mrknockknockgaming-droid/hvac-monitor/design/fullscope-home-mockup.html

Continuous diagnostics & control

HomeMain floor heat pump

LIVEUpdated 2:32 pmDetails for your technician →

Check soonCooling · running for 42 min

# Your system is cooling, but air may be restricted

Air isn't moving through your system as freely as it should. This is most often a dirty air filter — your filter was last changed 94 days ago.

What should I do?Request service

Inside77°FAir returning to the system

Outside104°FMesa, AZ

Air from vents56°F21° cooler than inside

Running today6.4hr9 cycles

## What we noticed

Checked continuously while your system runs

Check soonAir may be restrictedMost often a dirty filter. Easy to check yourself.▶

#### What we're seeing

Air is pushing against more resistance than your equipment is designed for. It started at 1:54 pm today and also happened on Friday.

#### Why it matters

Your system works harder, cools less and uses more electricity. Left alone for a long time, it can freeze the indoor coil or wear out the blower.

#### What you can do

1. Check your air filter and replace it if it looks grey or dusty.
2. Make sure vents and return grilles aren't closed or blocked by furniture.
3. We'll recheck on the next cycle. If this is still showing tomorrow, request a service visit.

For your contractor: external static 0.72 in. w.c. (equipment maximum 0.50).

Good to knowCooling less than its rating in this heatExpected at 104 °F outside — no action on its own.▶

Every air conditioner delivers less cooling on very hot days. Yours is providing about 84 % of its rated cooling right now — partly because of the heat and partly because of the airflow issue above.

Fixing the airflow should bring this up.

Good to knowA monitoring sensor is disconnectedDoesn't affect heating or cooling. Your contractor has been notified.▶

One optional temperature sensor on the outdoor unit isn't reporting. Your system runs exactly the same without it; it only gives your technician extra information.

Since Thursday · Contractor notified

Refrigerant, outdoor unit and thermostat checks are normal.

## Maintenance

- Air filterDue nowChanged Jun 24 · 94 days ago · every 90 days
- Tune-upUp to dateLast visit Apr 2026 · next before heating season, Oct 2026

SH

Saguaro Heating & AirYour service contractor · (480) 555-0142

Request service

## System health

4 of 5 areas are good

- CoolingGood
  Air from your vents is about 21° cooler than the air going in — right where it should be.
- AirflowCheck soon
  Air is moving less freely than it should. See “Air may be restricted”.
- RefrigerantGood
  Pressures and temperatures look normal for today's weather.
- Outdoor unitGood
  Working hard in the heat, as expected. Releasing heat normally.
- MonitoringConnected
  Both monitors online. One optional sensor is offline — your contractor knows.

## Last 24 hours

Inside and outside temperature, and when your system ran

Inside Outside System running

Ran6.4 hr

Outside high105 °F

Inside average77 °F

FullscopeContinuous diagnostics & control· installed by Saguaro Heating & AirChecks run every 5 seconds while the system is on

Light / dark
