mrknockknockgaming-droid/hvac-monitor/design/fullscope-monitor-mockup.html

Main floor heat pumpHome · Mesa, AZ · 1,240 ft · R-410A · 3.5 ton

Mode

CoolingYGOW

Indoor node

Online 2 s

Outdoor node

Online 3 s

Last update14:32:08

Outdoor air103.8°F

Runtime42min cycle · 6.4h today

Diagnostics

1 warning2 advisory1 sensor

Superheatcalc

12.4°F

NormalTarget 8–15

Subcoolingcalc

9.7°F

NormalTarget 10 ± 3

Delta-Tcalc

21.2°F

Above targetTarget 16–21

Total ext. staticcalc

0.72in. w.c.

HighMax 0.50

Airflowcfg

1,400CFM

Manufacturer specUnverified

Total capacitycalc

34,900BTU/hr

84% of rated2.91 tons

Outdoor ambientmeas

103.8°F

RH 12 %Rating point 95

## Live trend

Shaded Y bar = compressor call · hover for values at a timestamp

Refrigerant Air side Pressure Temperature Performance All

15 min 1 hr 6 hr 24 hr 7 days

## Operating state

Cooling

Y Compressor | On 42 min
G Blower | On
O Reversing valve | Energized → cooling
W Aux heat | Off

Cycle start13:50:02

Cycles today9

Avg on-time38min

## Sensor health

Click a row for detail

Nodes
Indoor node | Online | 2 s
fw 0.1.0 · 192.168.1.121 · −55 dBm · up 3.2 d
Outdoor node | Online | 3 s
fw 0.1.0 · 192.168.1.247 · −61 dBm · up 3.2 d · 5 V rail 5.02 V
Pressure
Liquid line | OK | 50 bar
Vapor port | OK | 50 bar
True suction | Not installed | optional
Temperature
Suction · liquid | OK | 2 of 2
Supply · return air | OK | 2 of 2
Discharge | Open circuit | optional
ADS1115 0x49 A2 = 3.29 V — outside 0.30–3.00 V. Not used by any active diagnostic.
Humidity & static
Humidity ×3 | OK | 3 of 3
Static ×2 | OK | 2 of 2
Filter / coil ΔP | Not installed | optional

## Refrigerant performance

R-410A · TXV · cooling

Measurement | | Low side · suction | High side · liquid
Pressure | meas | 128.4psigVapor service port | 418.2psigLiquid line
Saturation temp | calc | 44.1°FEvaporator · dew | 120.0°FCondenser · bubble
Line temp | meas | 56.5°F | 110.3°F
Superheat / subcooling | calc | SH 12.4°FNormal · target 8–15 | SC 9.7°FNormal · target 10 ± 3

Cond. over ambient16.2°F

Liquid approach6.5°F

Compression ratio3.03: 1

RefrigerantR-410A

Metering deviceTXV

True suctionNot installed

## Air-side performance

Psychrometrics at 14.05 psia

Measurement | | Return | Supply | Difference
Dry bulb | meas | 77.2°F | 56.0°F | ΔT 21.2°FAbove · target 16–21
Relative humidity | meas | 44% | 86% | —
Wet bulb | calc | 62.3°F | 53.6°F | 8.7°F
Dew point | calc | 53.6°F | 51.9°F | 1.7°F
Enthalpy | calc | 28.54BTU/lb | 22.74BTU/lb | Δh 5.80

### Static pressure in. w.c., referenced to room

Return static | meas | −0.28in. w.c. | Between filter and blower
Supply static | meas | +0.44in. w.c. | Plenum, after coil
Filter pressure drop | meas | — | Not installed
Coil pressure drop | meas | — | Not installed

Total external static calc

0.72in. w.c.

High · 144 % of max

Max 0.50 (equipment)

00.250.500.751.00

|−0.28| + 0.44 = 0.72 · limit from Equipment → Max external static

## System capacity

Enthalpy method

Equipment airflow CFM cfg

Source Equipment →

Total capacity

34,900BTU/hr

2.91tons

Sensible | 30,600BTU/hr
Latent | 4,300BTU/hr
Sensible heat ratio | 0.88
Airflow per ton | 400CFM/ton

4.5 × CFM × Δh and 1.08 × CFM × ΔT, density-corrected for 1,240 ft (× 0.956). Rounded to 100 BTU/hr — accuracy is limited by the airflow value.

% of rated 84%

0Rated 41,500 BTU/hr at 95 °F OD120 %

## System diagnostics

0 fault1 warning2 advisory1 sensor error4 normal

Judged after 10 min of steady running · inferences, not confirmed diagnoses Show normal

| Severity | System | Condition | Evidence | Possible causes | Status | Since
▸ | Warning | Air side | Possible airflow restriction — high external static | TESP 0.72in. w.c.max 0.50 | Coil restriction · restrictive supply duct · filter · blower tap | Active | 13:54
What triggered it Rule AF-02: total external static above the configured maximum (0.50 in. w.c.) for more than 5 min with the blower running. Interpretation only — a possible airflow restriction, not a confirmed fault. TESP, last 60 min · dashed = max 0.50 Current vs expected

Measurement | Current | Expected
TESP | 0.72in. w.c. | ≤ 0.50
Supply static | +0.44in. w.c. | —
Return static | −0.28in. w.c. | —
Delta-T | 21.2°F | 16–21
Superheat | 12.4°F | 8–15
Airflow (configured) | 1,400CFM | unverified

#### How long

First detected | 13:54:10
Duration | 38 min, continuous
Cycles today | 7 of 9
Previous event | Fri 25 Sep

#### Possible causes · ranked by evidence

1. Evaporator coil restriction — supply side carries 61 % of TESP
2. Restrictive supply duct, closed registers or dampers
3. Filter restriction — less likely; return static is moderate
4. Blower speed tap above duct design

Filter and coil ΔP probes would separate causes 1 and 3.

AcknowledgeAdd noteShow in trend
▸ | Advisory | Air side | Delta-T above target range | ΔT 21.2°Ftarget 16–21 | Reduced airflow · blower tap | Active | 14:01
What triggered it Rule AS-04: delta-T above the target band for the return humidity (16–21 °F at 44 % RH) for more than 10 min. Delta-T, last 60 min · dashed = 21 °F Current vs expected

Measurement | Current | Expected
Delta-T | 21.2°F | 16–21
Return RH | 44% | —
TESP | 0.72in. w.c. | ≤ 0.50
Superheat | 12.4°F | 8–15

#### How long

First detected | 14:01:40
Duration | 31 min

#### Possible causes

1. Reduced airflow — consistent with high TESP
2. Blower speed tap set low

AcknowledgeShow in trend
▸ | Advisory | Capacity | Capacity below rated | 34,900BTU/hr84 % of 41,500 | Reduced airflow · high ambient · airflow unverified | Active | 14:02
What triggered it Rule CP-01: measured total capacity below 90 % of rated for more than 15 min. Depends on the configured airflow. If actual airflow is lower than 1,400 CFM, measured capacity is lower still. Current vs expected

Measurement | Current | Expected
Total capacity | 34,900BTU/hr | ≥ 37,400
Rated capacity | 41,500BTU/hr | at 95 °F OD
Outdoor ambient | 103.8°F | 95 rating pt.
Airflow source | Manufacturer | measured

#### How long

First detected | 14:02:15
Duration | 30 min

#### Possible causes

1. Reduced airflow — see static pressure
2. Outdoor ambient 8.8 °F above rating point
3. Airflow value not verified on site

▸ | Sensor error | Sensors | Discharge temperature probe open circuit | 0x49 A2 3.29V | Unplugged · broken lead · not fitted | Acknowledged | Thu
What triggered it Channel t_dis reads outside its physical range (≥ 3.25 V = open circuit). A measurement problem, not an equipment problem. No active diagnostic depends on this channel. Current vs expected

Measurement | Current | Expected
ADS1115 0x49 A2 | 3.29V | 0.30–3.00
Configured as | Optional | —

#### How long

Since | Thu 24 Sep 09:12
Acknowledged | Thu 24 Sep 09:40

#### Possible causes

1. Probe connector unplugged
2. Broken lead
3. Probe not fitted yet

Mark not installed
| Normal | Refrigerant | Superheat within target | SH 12.4°Ftarget 8–15 | — | Normal
| Normal | Refrigerant | Subcooling within target | SC 9.7°Ftarget 10 ± 3 | — | Normal
| Normal | Condenser | Condensing over ambient within range | CTOA 16.2°Ftarget 12–25 | — | Normal
| Normal | Nodes | Both nodes reporting | 2 s3 s | — | Normal

FullscopeContinuous diagnostics & control meas measured by a sensor calc calculated from measurements cfg configured in Equipment Interpretation appears only in status words and the diagnostics table. server 0.1.0 · MQTT 192.168.1.191:1883 · stored 90 d

## Equipment configuration

Main floor heat pump · values here feed the calculations on Monitor

CancelSave configuration

## Identification

Field | Value | Used by
Manufacturer
Outdoor model
Indoor model
Serial number
Installed

## System

Field | Value | Used by
System type | | Mode logic
Heat pump / straight cool | | Mode logic
O/B configuration | | Mode detection
Nominal tonnage | tons | CFM/ton, estimated airflow
Refrigerant | | Saturation temps, SH, SC
Metering device | | SH/SC targets, rules

## Ratings & targets

Field | Value | Used by
Rated cooling capacity | BTU/hr | % of rated
Rated airflow | CFM | Airflow source: manufacturer
Configured airflow | CFM | Capacity (source: manufacturer)
Max external static | in. w.c. | TESP limit, rule AF-02
Superheat target | °F | Rule RF-01
Subcooling target | °F | Rule RF-02

## Site

Field | Value | Used by
Site elevation | ft | Atmospheric pressure, air density
Atmospheric pressure | 14.05psia derived | psig → psia for PT tables
Required sensors | | Missing = fault; others = unavailable

Light / dark
