mrknockknockgaming-droid/hvac-monitor/docs/hvac-schematics.html

# HVAC monitor wiring schematics

Prototype rev A for the outdoor refrigerant node and indoor air node. Net labels with the same name are connected. Red nets carry 24 VAC.

Signal netPower rail24 VAC netFuture / not fitted

## Outdoor node

Refrigerant pressures, line temperatures, outdoor air and mode sensing.

Sheet

1 of 2

Rev

A

Date

2026-09-24

Status

Prototype

APower supply 24 VAC from the unit, half-wave rectified, bucked to 5 V.

BController ESP32 pin assignments. Pins marked × are not connected.

CI²C devices Two ADCs and the outdoor air sensor share one bus.

DAnalog inputs Pressure dividers, 5 V rail monitor and pipe thermistors.

EMode inputs Opto-isolated sensing of the Y and O/B calls.

Bill of materials

Ref | Part | Qty
U1 | ESP32 DevKit, 30-pin | 1
U2 | LM2596HV buck module | 1
U3, U4 | ADS1115 ADC module | 2
U5, U6 | H11AA1 AC-input optocoupler | 2
F1 | 0.5 A fast-blow fuse + holder | 1
D1 | SMBJ48CA bidirectional TVS | 1
D2 | 1N4007 rectifier | 1
C1 | 470 µF 63 V electrolytic | 1
C2–C8 | 0.1 µF ceramic | 7
R1, R3, R5, R7 | 10k 1% metal film | 4
R2, R4, R6 | 20k 1% metal film | 3
R8 | 15k 1% metal film | 1
R9, R10 | 10k 0.1% (or 1%) | 2
R11, R13 | 4.7k ½ W | 2
R12, R14 | 10k ¼ W | 2
TH1, TH2 | DROK 10k NTC B3950 | 2
J1, J2 | 2-pin 5.08 mm terminal | 2
J3–J5 | 3-pin terminal (XDB307) | 3
J6, J7 | 2-pin terminal (thermistors) | 2
J8 | 4-pin terminal (SHT30) | 1
— | XDB307-3 transducers (2 now, 1 later) | 3
— | FS400-SHT30 probe | 1

## Indoor node

Supply and return air temperatures and thermostat mode sensing.

Sheet

2 of 2

Rev

A

Date

2026-09-24

Status

Prototype

APower supply Identical to the outdoor node.

BController ESP32 pin assignments. Pins marked × are not connected.

C1-Wire temperatures Supply and return air probes on one bus.

DMode inputs Opto-isolated sensing of Y, W, G and O/B.

EExpansion Reserved for static pressure and humidity sensors.

Bill of materials

Ref | Part | Qty
U1 | ESP32 DevKit, 30-pin | 1
U2 | LM2596HV buck module | 1
U3–U6 | H11AA1 AC-input optocoupler | 4
F1 | 0.5 A fast-blow fuse + holder | 1
D1 | SMBJ48CA bidirectional TVS | 1
D2 | 1N4007 rectifier | 1
C1 | 470 µF 63 V electrolytic | 1
C2 | 0.1 µF ceramic | 1
R1 | 4.7k ¼ W (1-Wire pull-up) | 1
R2, R4, R6, R8 | 4.7k ½ W | 4
R3, R5, R7, R9 | 10k ¼ W | 4
J1 | 2-pin 5.08 mm terminal | 1
J2 | 4-pin terminal (Y, W, G, O/B) | 1
J3, J4 | 3-pin terminal (DS18B20) | 2
J5 | 4-pin header (future, DNP) | 1
— | DS18B20 probes | 2

## General notes

1. C from the equipment transformer is system ground. Tie C, buck output −, ESP32 GND and all sensor grounds together.
2. Set each LM2596HV to 5.00 V with a meter before connecting the ESP32 or sensors.
3. Never have USB and 24 VAC connected at the same time while flashing.
4. All 0.1 µF filter capacitors mount directly at the ADS1115 input pins.
5. Mount the ESP32 in a plastic enclosure outside sheet-metal cabinets so the PCB antenna can reach WiFi.
