mrknockknockgaming-droid/hvac-monitor/project-files/3-screenshots/1-first-web-app-sep29/01-homeowner-home-cooling-normally.jpg

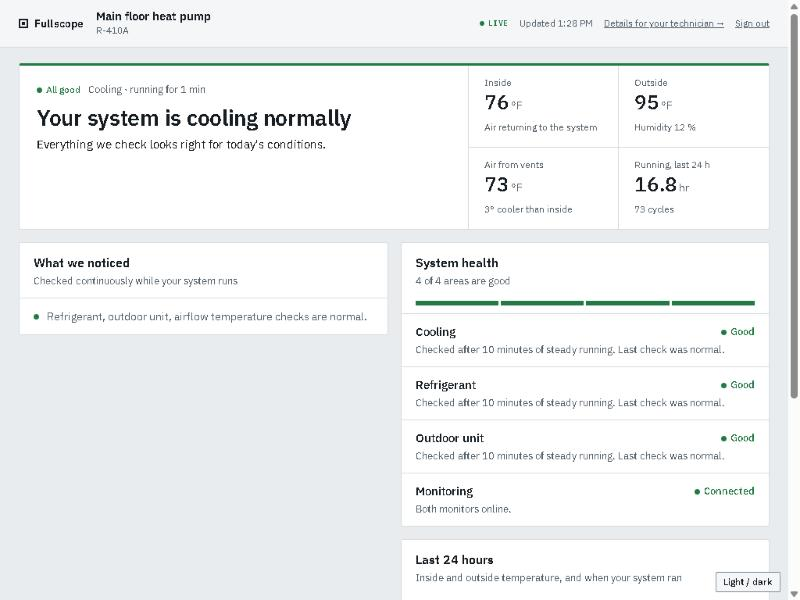
project-files/3-screenshots/1-first-web-app-sep29/01-homeowner-home-cooling-normally.jpg
