mrknockknockgaming-droid/hvac-monitor/project-files/3-screenshots/1-first-web-app-sep29/02-homeowner-last-24-hours-chart.jpg

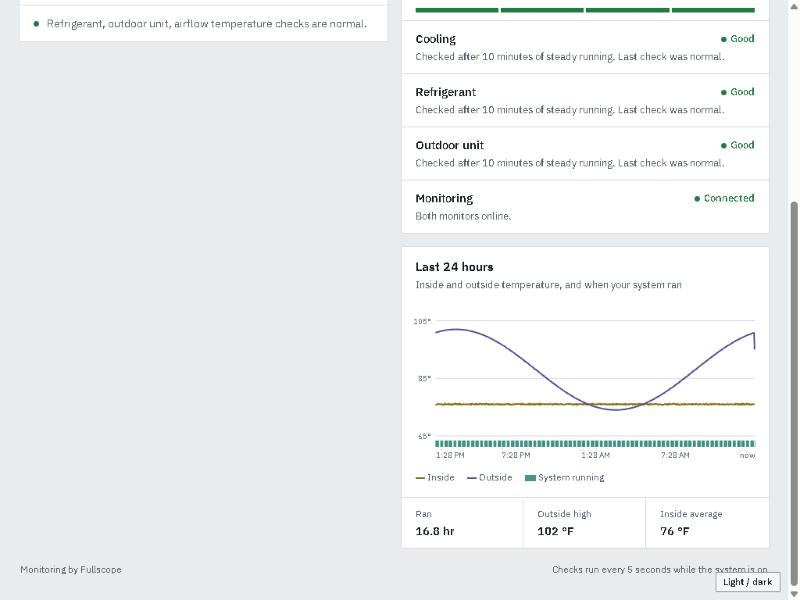
project-files/3-screenshots/1-first-web-app-sep29/02-homeowner-last-24-hours-chart.jpg
