mrknockknockgaming-droid/hvac-monitor/project-files/3-screenshots/1-first-web-app-sep29/03-technician-monitor.jpg

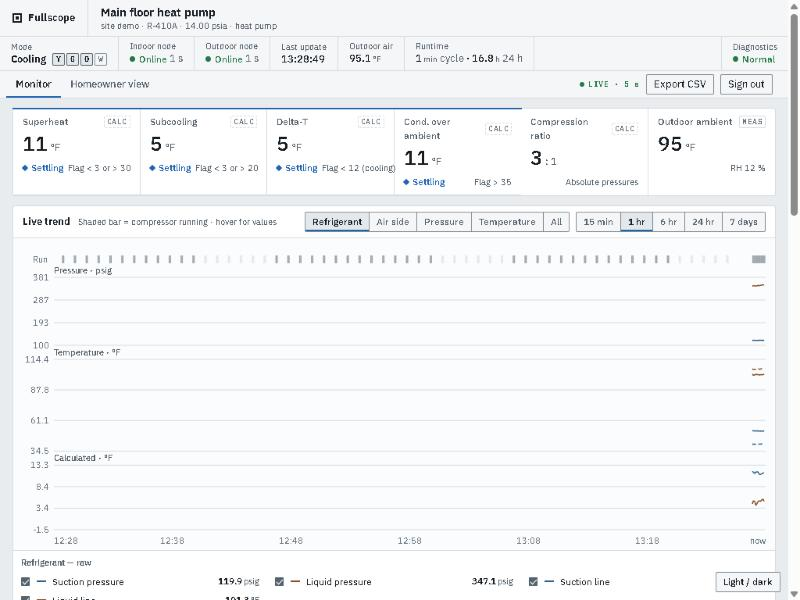
project-files/3-screenshots/1-first-web-app-sep29/03-technician-monitor.jpg
