mrknockknockgaming-droid/hvac-monitor/project-files/3-screenshots/1-first-web-app-sep29/04-technician-monitor-compressor-cycles.jpg

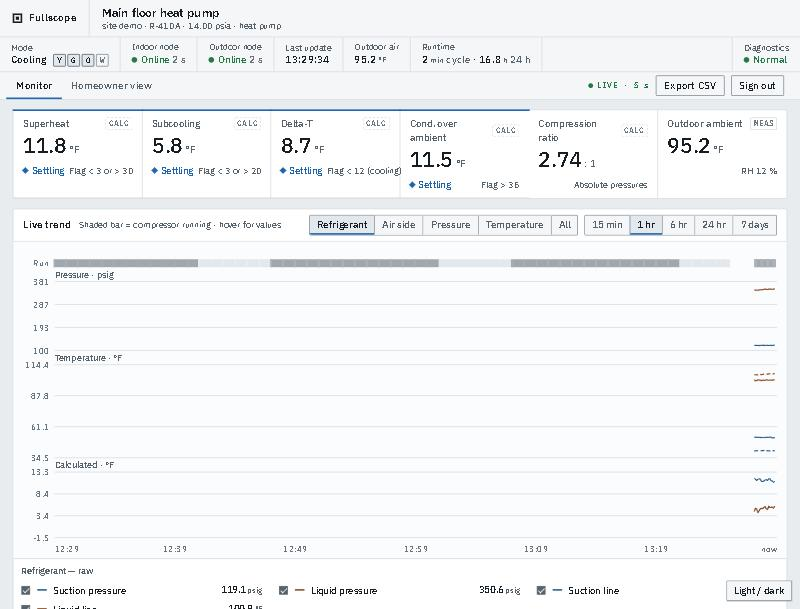
project-files/3-screenshots/1-first-web-app-sep29/04-technician-monitor-compressor-cycles.jpg
