mrknockknockgaming-droid/hvac-monitor/project-files/3-screenshots/1-first-web-app-sep29/05-trend-24h-hover-readout.jpg

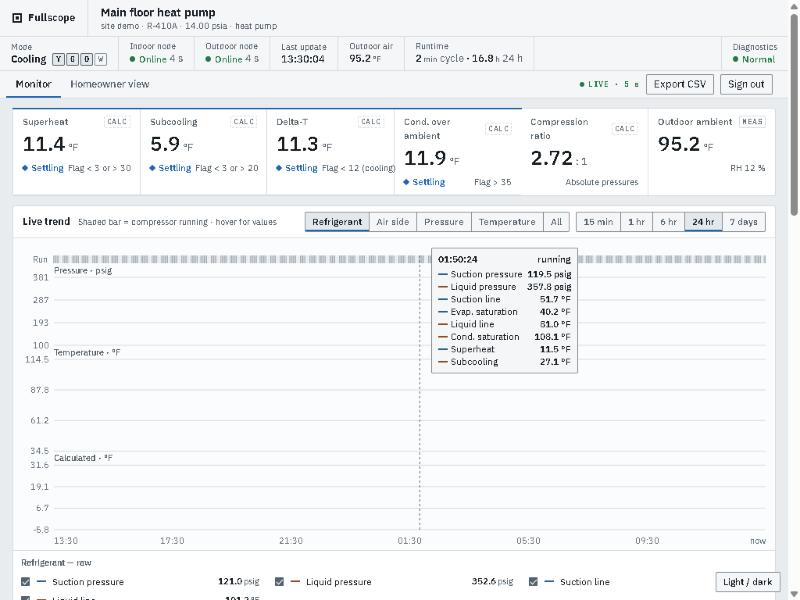
project-files/3-screenshots/1-first-web-app-sep29/05-trend-24h-hover-readout.jpg
