mrknockknockgaming-droid/hvac-monitor/project-files/3-screenshots/1-first-web-app-sep29/06-trend-24h-pressure-cycles.jpg

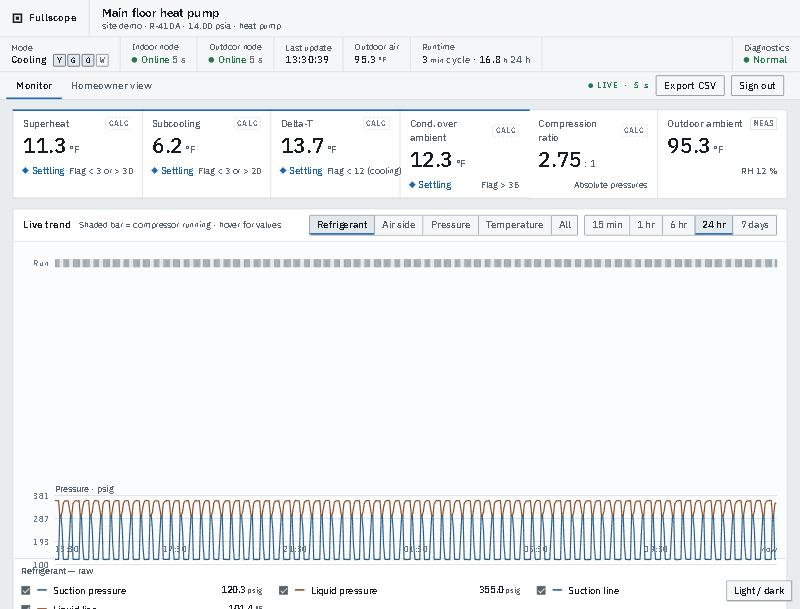
project-files/3-screenshots/1-first-web-app-sep29/06-trend-24h-pressure-cycles.jpg
