mrknockknockgaming-droid/hvac-monitor/project-files/3-screenshots/1-first-web-app-sep29/07-trend-air-side.jpg

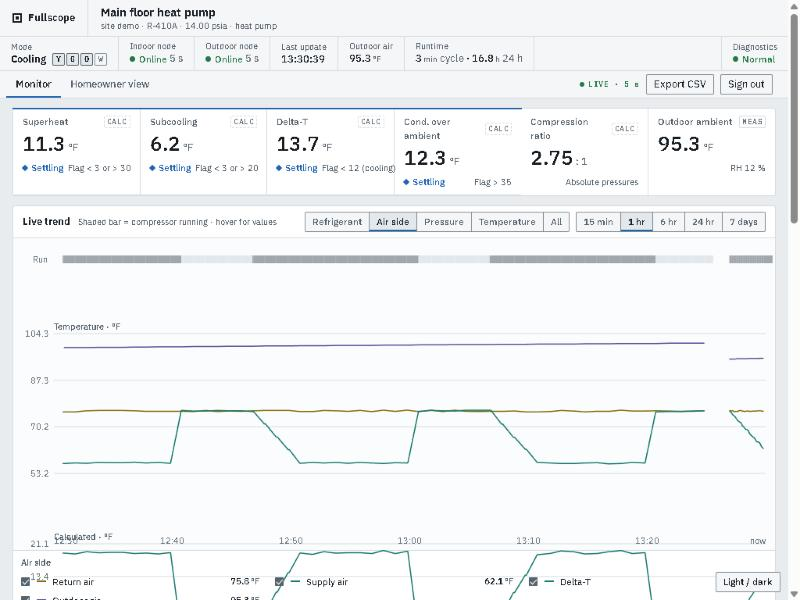
project-files/3-screenshots/1-first-web-app-sep29/07-trend-air-side.jpg
