mrknockknockgaming-droid/hvac-monitor/project-files/3-screenshots/1-first-web-app-sep29/08-trend-air-side-delta-t.jpg

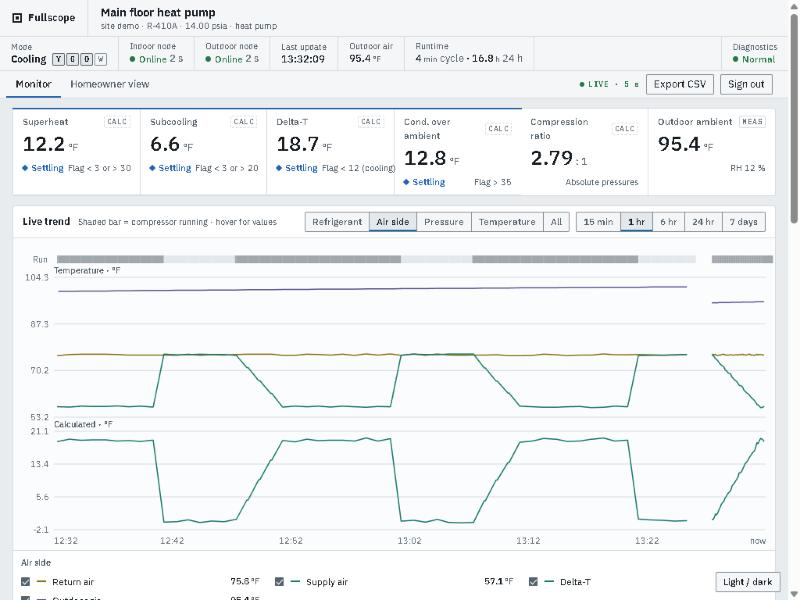
project-files/3-screenshots/1-first-web-app-sep29/08-trend-air-side-delta-t.jpg
