mrknockknockgaming-droid/hvac-monitor/project-files/3-screenshots/1-first-web-app-sep29/10-technician-refrigerant-and-air-tables.jpg

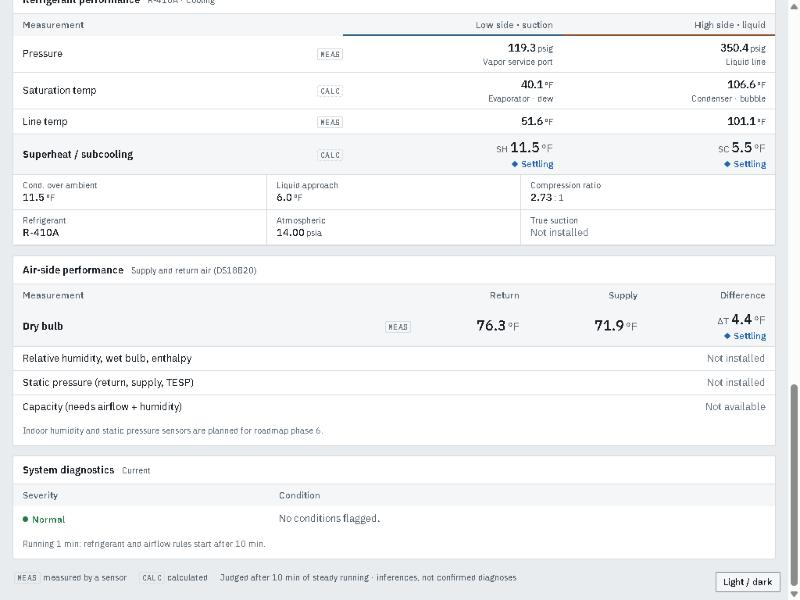
project-files/3-screenshots/1-first-web-app-sep29/10-technician-refrigerant-and-air-tables.jpg
