mrknockknockgaming-droid/hvac-monitor/project-files/3-screenshots/1-first-web-app-sep29/11-homeowner-sensor-advisory.jpg

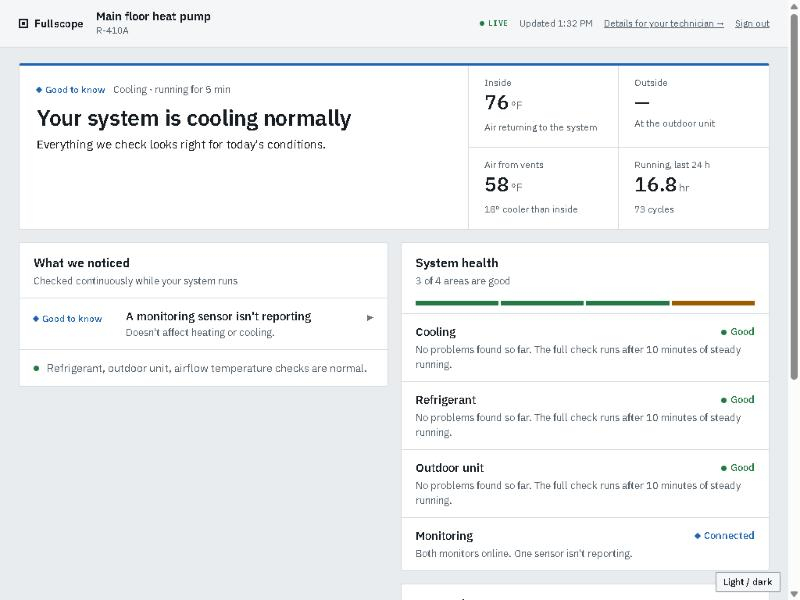
project-files/3-screenshots/1-first-web-app-sep29/11-homeowner-sensor-advisory.jpg
