mrknockknockgaming-droid/hvac-monitor/project-files/3-screenshots/1-first-web-app-sep29/12-technician-dark-theme-sensor-error.jpg

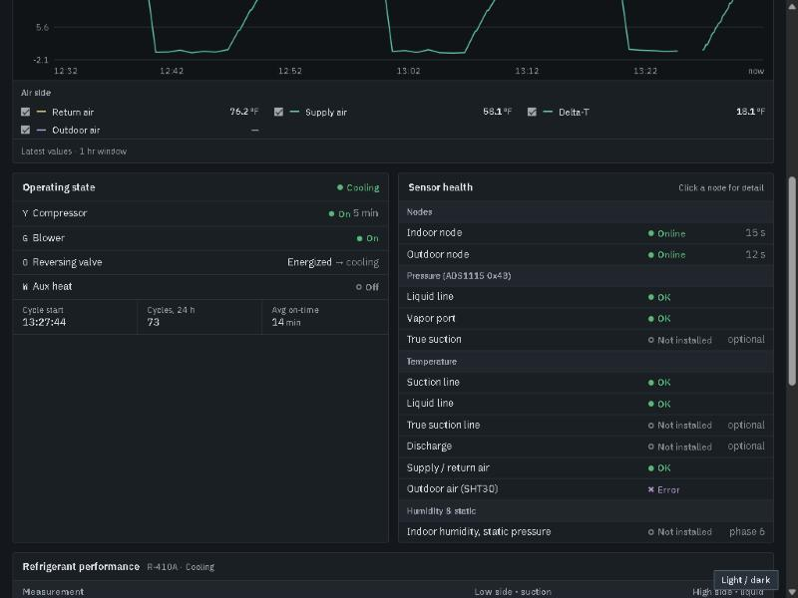
project-files/3-screenshots/1-first-web-app-sep29/12-technician-dark-theme-sensor-error.jpg
