mrknockknockgaming-droid/hvac-monitor/project-files/3-screenshots/2-fullscope-redesign-oct2/03-technician-monitor-dark.jpg

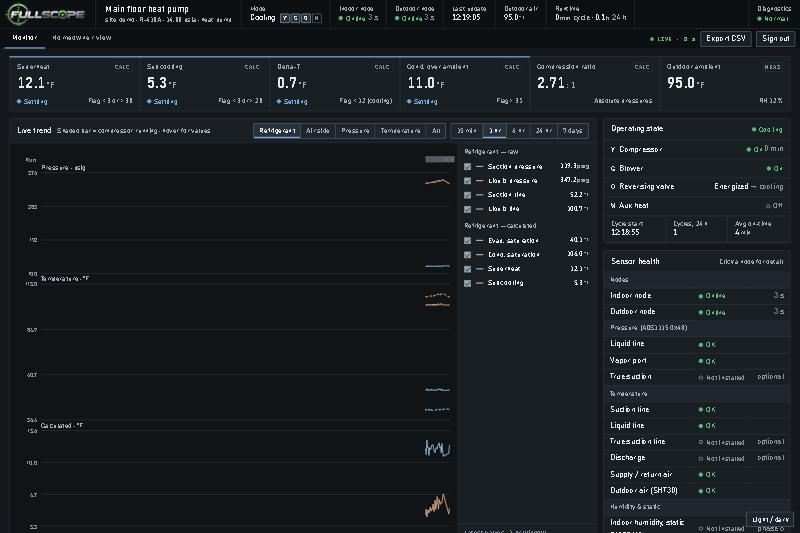
project-files/3-screenshots/2-fullscope-redesign-oct2/03-technician-monitor-dark.jpg
