mrknockknockgaming-droid/hvac-monitor/project-files/3-screenshots/2-fullscope-redesign-oct2/04-homeowner-light-all-good.jpg

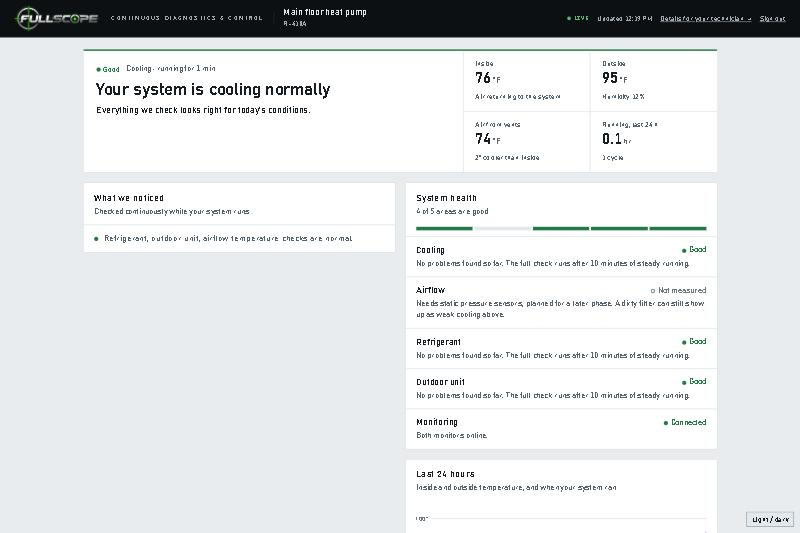
project-files/3-screenshots/2-fullscope-redesign-oct2/04-homeowner-light-all-good.jpg
