mrknockknockgaming-droid/hvac-monitor/project-files/3-screenshots/3-technician-tools/01-alert-log.jpg

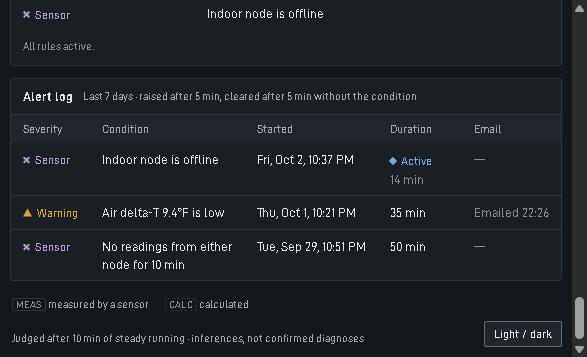
project-files/3-screenshots/3-technician-tools/01-alert-log.jpg
