mrknockknockgaming-droid/hvac-monitor/project-files/3-screenshots/5-accounts-and-fleet/01-email-password-sign-in.jpg

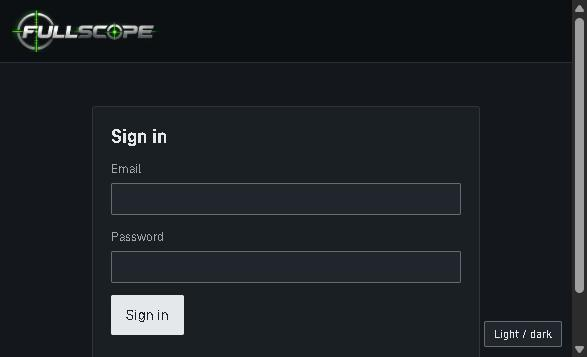
project-files/3-screenshots/5-accounts-and-fleet/01-email-password-sign-in.jpg
