mrknockknockgaming-droid/hvac-monitor/project-files/3-screenshots/5-accounts-and-fleet/02-contractor-fleet-page.jpg

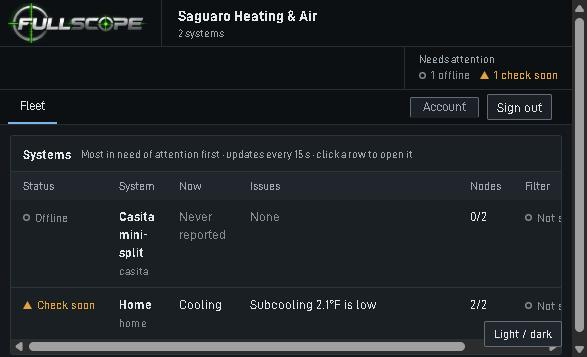
project-files/3-screenshots/5-accounts-and-fleet/02-contractor-fleet-page.jpg
