mrknockknockgaming-droid/hvac-monitor/project-files/3-screenshots/6-contractor-demo/01-demo-fleet-worst-first.jpg

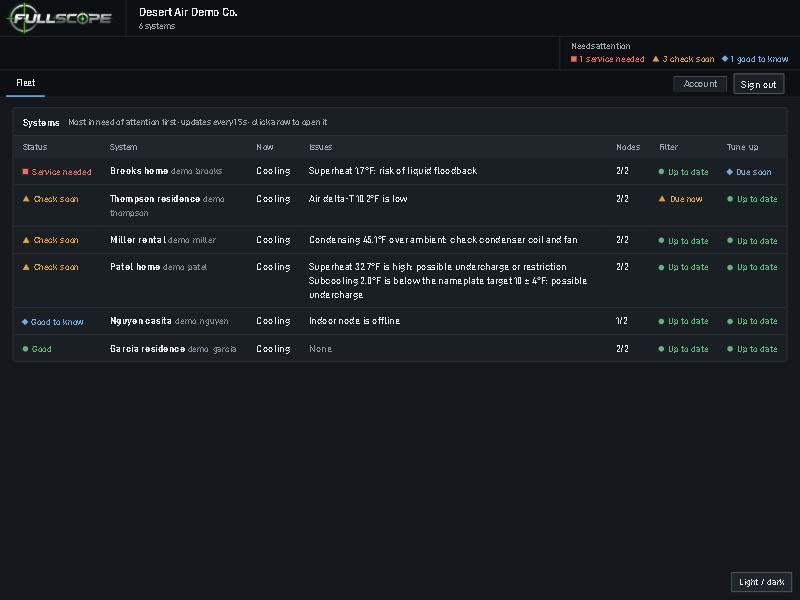
project-files/3-screenshots/6-contractor-demo/01-demo-fleet-worst-first.jpg
