mrknockknockgaming-droid/hvac-monitor/project-files/3-screenshots/6-contractor-demo/02-brooks-home-floodback.jpg

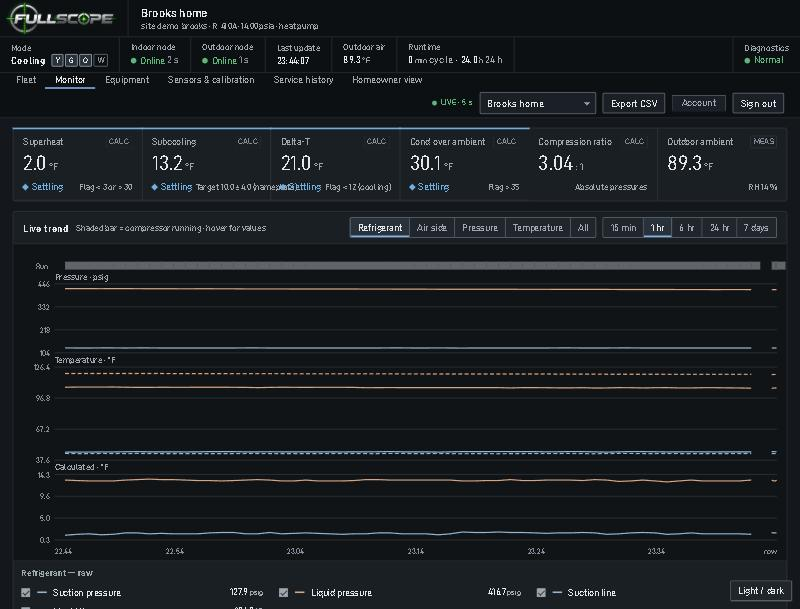
project-files/3-screenshots/6-contractor-demo/02-brooks-home-floodback.jpg
