mrknockknockgaming-droid/hvac-monitor/project-files/3-screenshots/6-contractor-demo/03-rivera-thermostat-screen-home.jpg

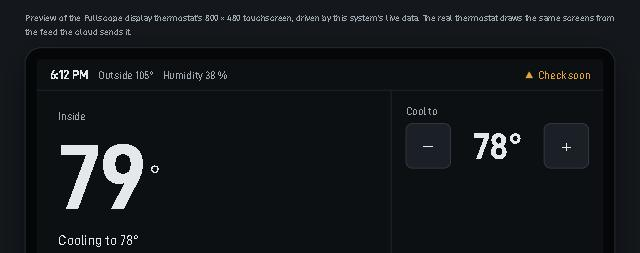
project-files/3-screenshots/6-contractor-demo/03-rivera-thermostat-screen-home.jpg
