mrknockknockgaming-droid/hvac-monitor/project-files/3-screenshots/6-contractor-demo/04-rivera-thermostat-service-capacitor-marker.jpg

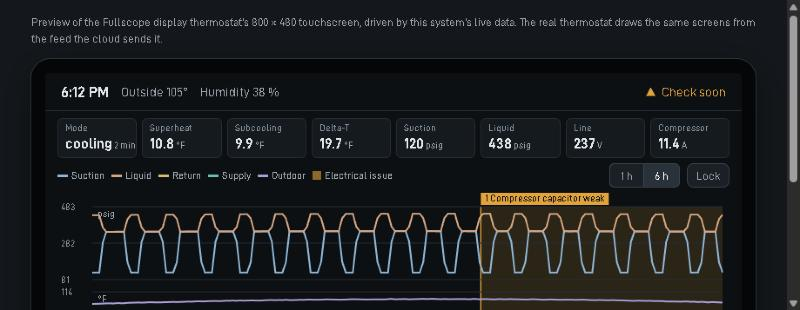
project-files/3-screenshots/6-contractor-demo/04-rivera-thermostat-service-capacitor-marker.jpg
