mrknockknockgaming-droid/hvac-monitor/project-files/3-screenshots/7-thermostat-web/01-homeowner-thermostat-card.jpg

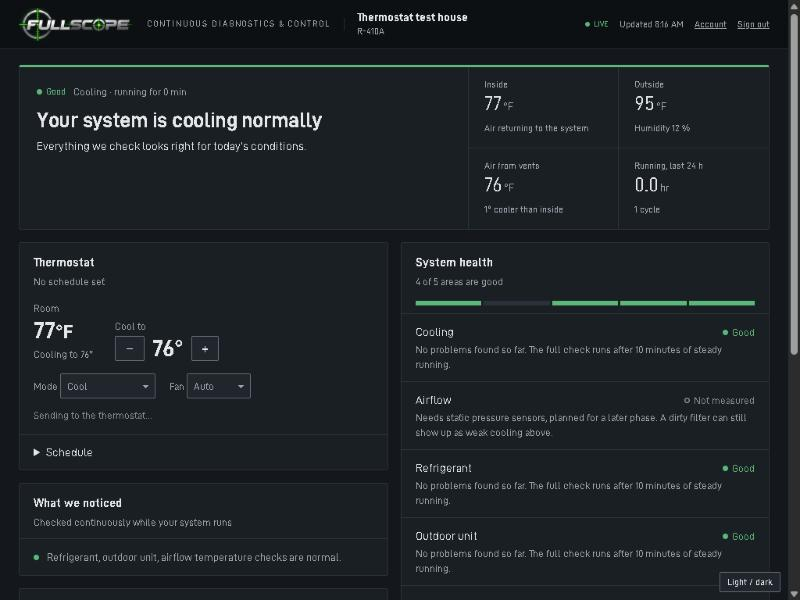
project-files/3-screenshots/7-thermostat-web/01-homeowner-thermostat-card.jpg
