mrknockknockgaming-droid/hvac-monitor/project-files/3-screenshots/7-thermostat-web/02-setpoint-hold.jpg

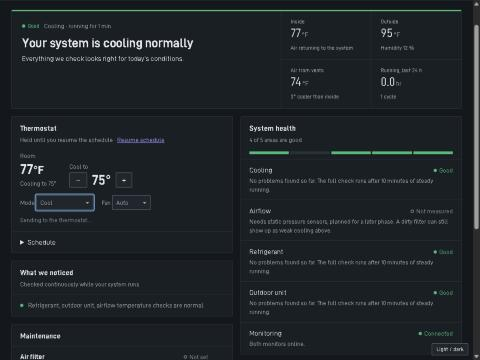
project-files/3-screenshots/7-thermostat-web/02-setpoint-hold.jpg
