mrknockknockgaming-droid/hvac-monitor/project-files/3-screenshots/7-thermostat-web/03-schedule-editor-empty.jpg

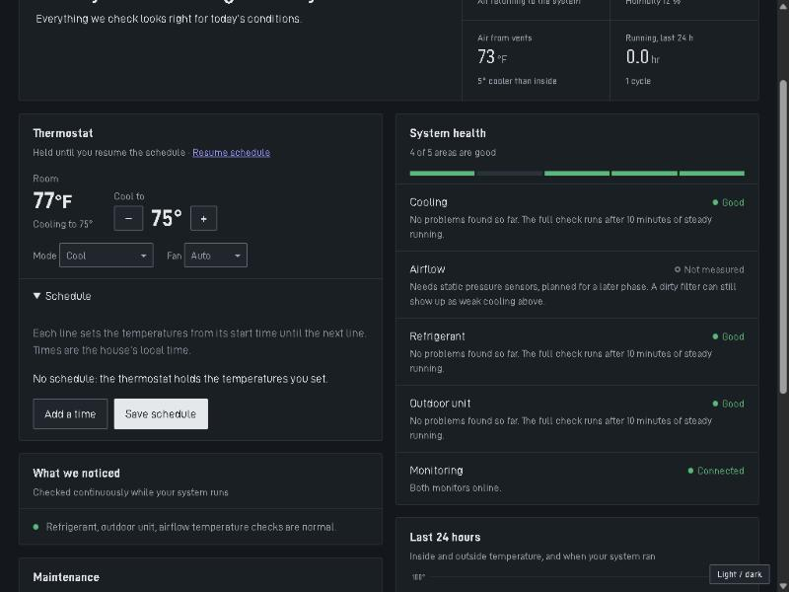
project-files/3-screenshots/7-thermostat-web/03-schedule-editor-empty.jpg
