mrknockknockgaming-droid/hvac-monitor/project-files/3-screenshots/7-thermostat-web/05-schedule-saved.jpg

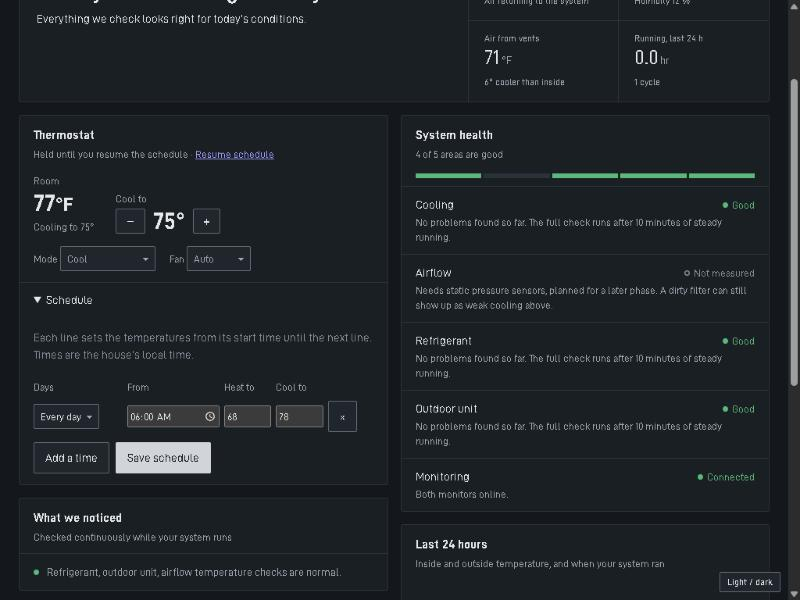
project-files/3-screenshots/7-thermostat-web/05-schedule-saved.jpg
