mrknockknockgaming-droid/hvac-monitor/project-files/3-screenshots/7-thermostat-web/06-following-schedule-minimum-run.jpg

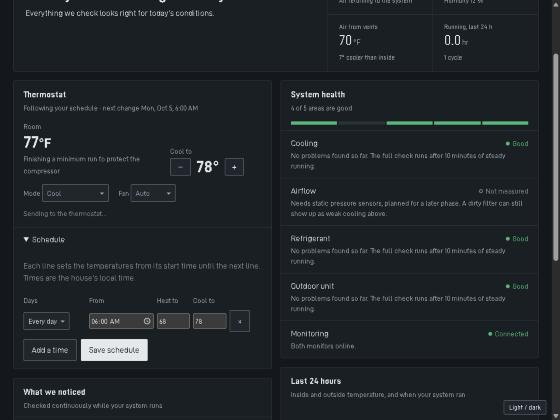
project-files/3-screenshots/7-thermostat-web/06-following-schedule-minimum-run.jpg
