mrknockknockgaming-droid/hvac-monitor/project-files/3-screenshots/7-thermostat-web/07-technician-thermostat-rows.jpg

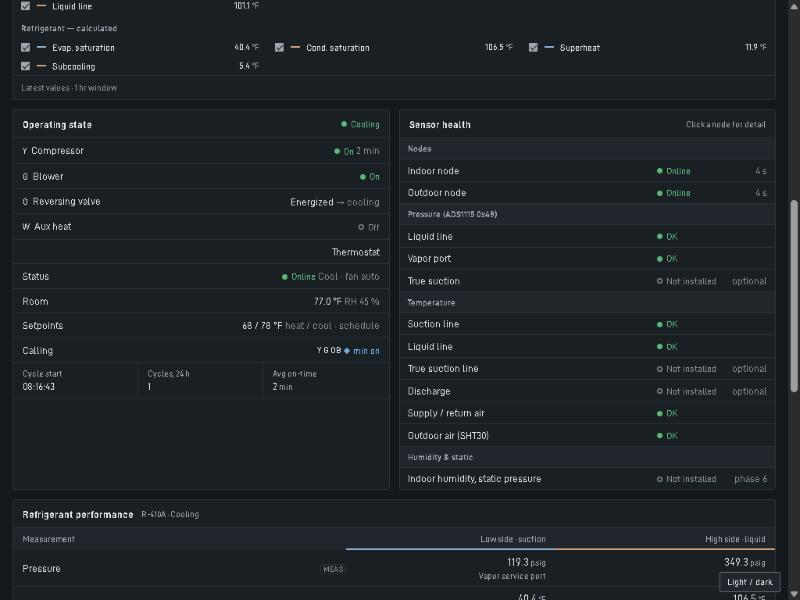
project-files/3-screenshots/7-thermostat-web/07-technician-thermostat-rows.jpg
