mrknockknockgaming-droid/hvac-monitor/project-files/3-screenshots/7-thermostat-web/08-equipment-thermostat-safety-settings.jpg

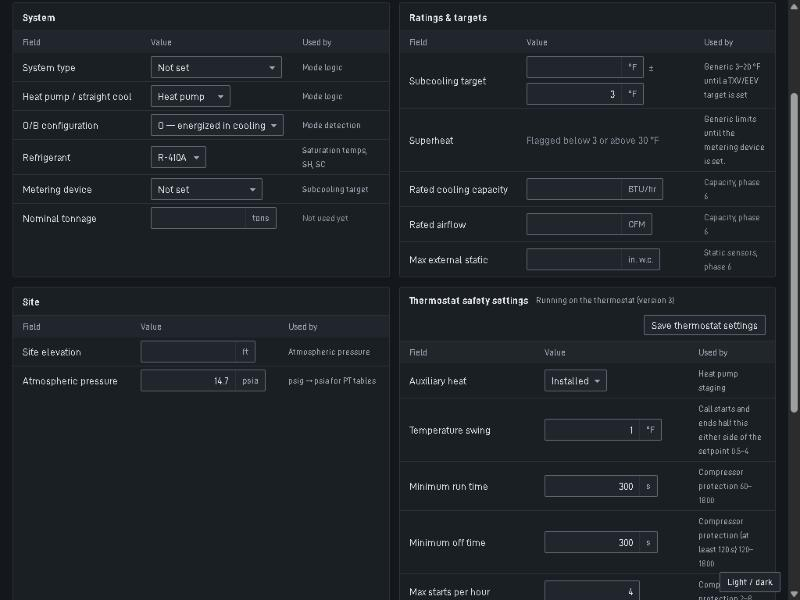
project-files/3-screenshots/7-thermostat-web/08-equipment-thermostat-safety-settings.jpg
