mrknockknockgaming-droid/hvac-monitor/project-files/3-screenshots/7-thermostat-web/09-equipment-thermostat-safety-settings-2.jpg

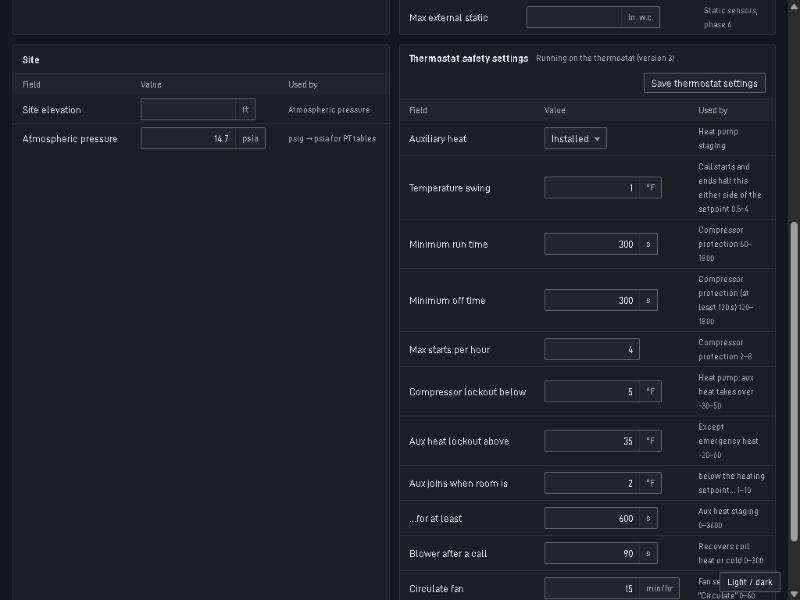
project-files/3-screenshots/7-thermostat-web/09-equipment-thermostat-safety-settings-2.jpg
