mrknockknockgaming-droid/hvac-monitor/project-files/3-screenshots/7-thermostat-web/10-thermostat-card-phone-width.jpg

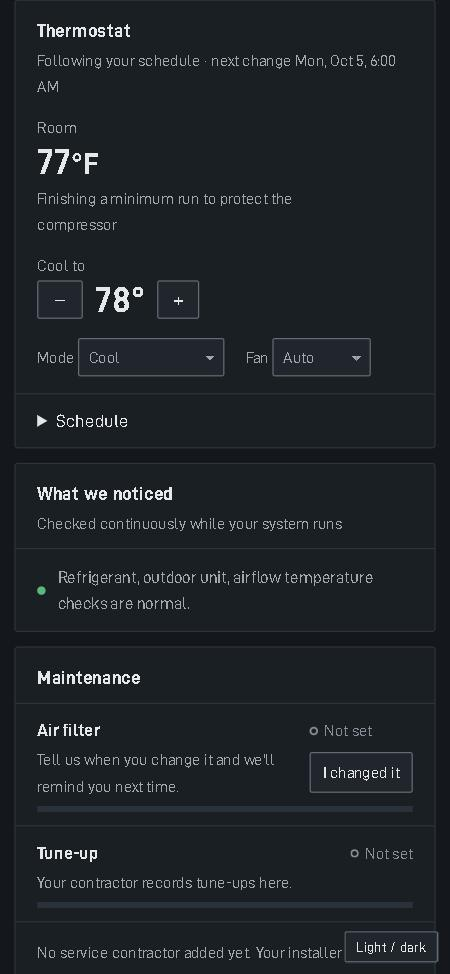
project-files/3-screenshots/7-thermostat-web/10-thermostat-card-phone-width.jpg
