mrknockknockgaming-droid/hvac-monitor/project-files/3-screenshots/8-thermostat-screen/01-home.jpg

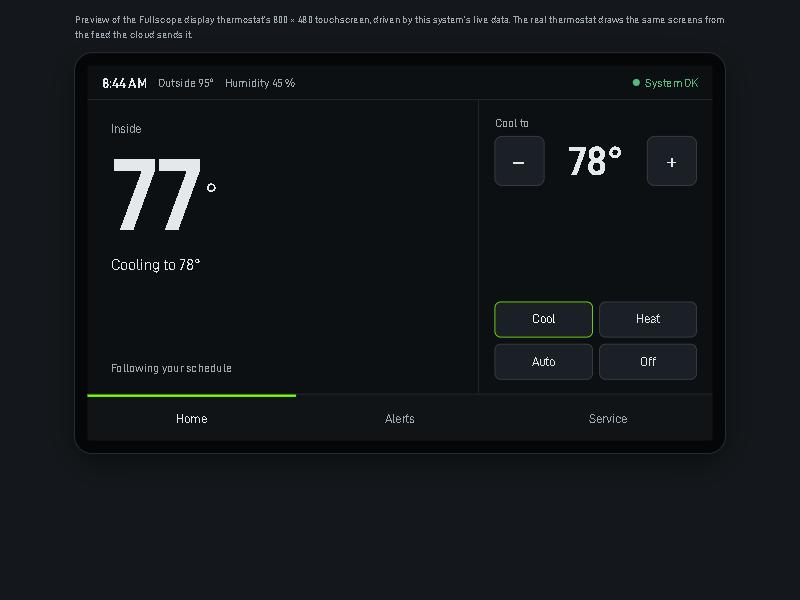
project-files/3-screenshots/8-thermostat-screen/01-home.jpg
