mrknockknockgaming-droid/hvac-monitor/project-files/3-screenshots/8-thermostat-screen/02-alerts-plain-language.jpg

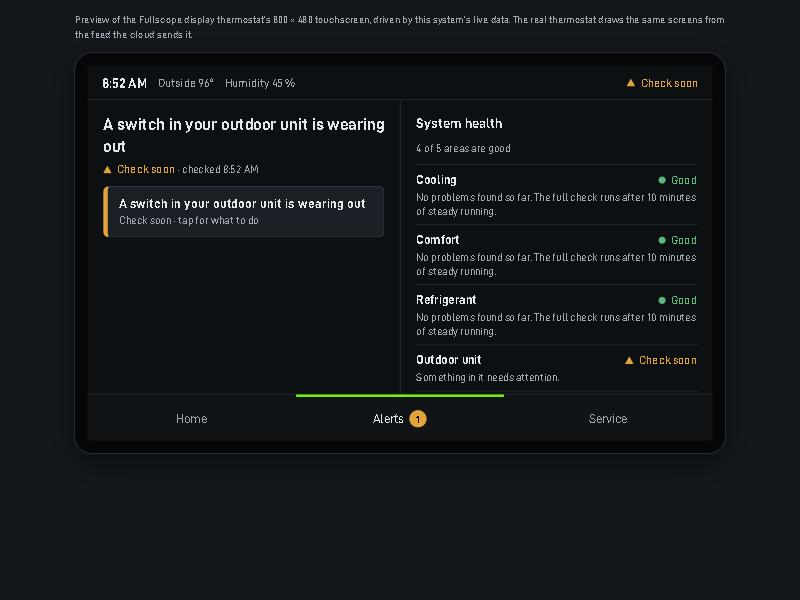
project-files/3-screenshots/8-thermostat-screen/02-alerts-plain-language.jpg
