mrknockknockgaming-droid/hvac-monitor/project-files/3-screenshots/8-thermostat-screen/03-alerts-system-health.jpg

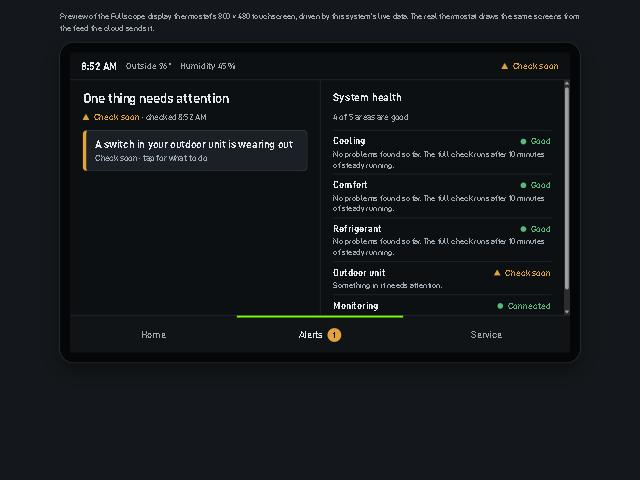
project-files/3-screenshots/8-thermostat-screen/03-alerts-system-health.jpg
