mrknockknockgaming-droid/hvac-monitor/project-files/3-screenshots/8-thermostat-screen/04-alert-detail-what-to-do.jpg

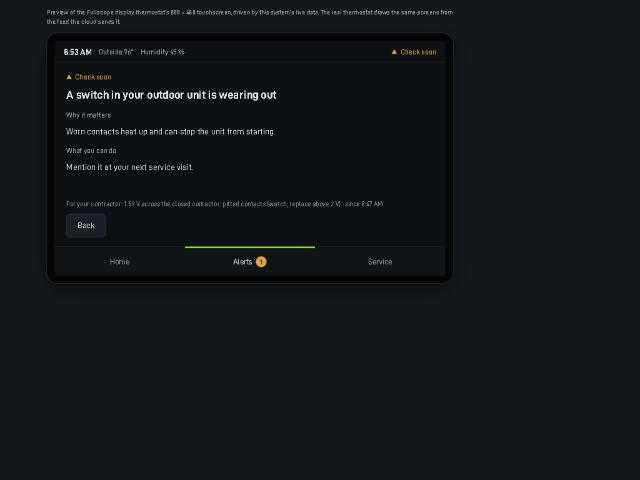
project-files/3-screenshots/8-thermostat-screen/04-alert-detail-what-to-do.jpg
