mrknockknockgaming-droid/hvac-monitor/project-files/3-screenshots/9-electrical-module/01-technician-electrical-rows-weak-capacitor.jpg

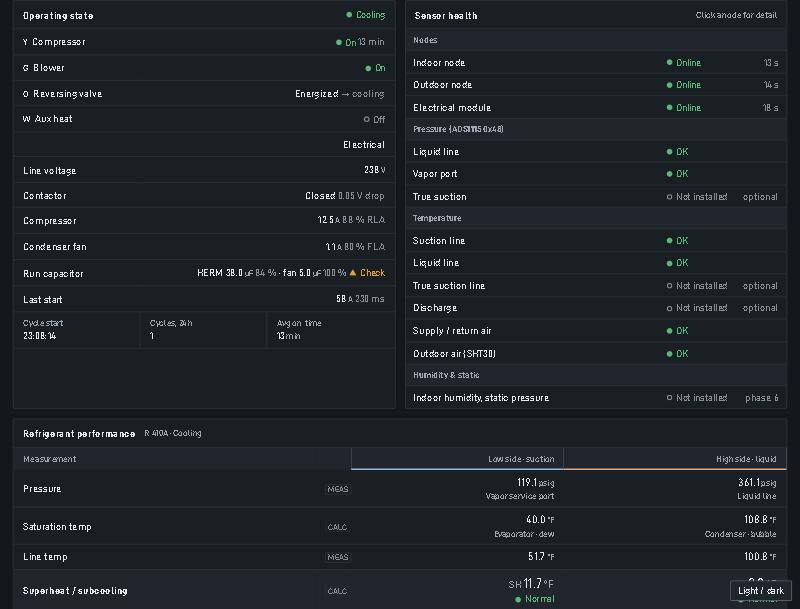
project-files/3-screenshots/9-electrical-module/01-technician-electrical-rows-weak-capacitor.jpg
