mrknockknockgaming-droid/hvac-monitor/project-files/3-screenshots/1-first-web-app-sep29/09-technician-operating-state-sensor-health.jpg

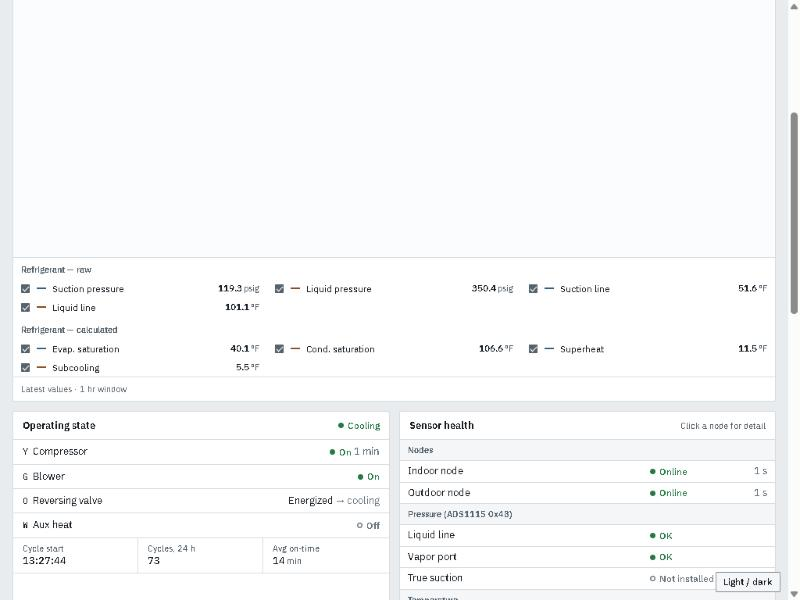
project-files/3-screenshots/1-first-web-app-sep29/09-technician-operating-state-sensor-health.jpg
