mrknockknockgaming-droid/hvac-monitor/project-files/3-screenshots/3-technician-tools/02-sensors-and-calibration-zero-span.jpg

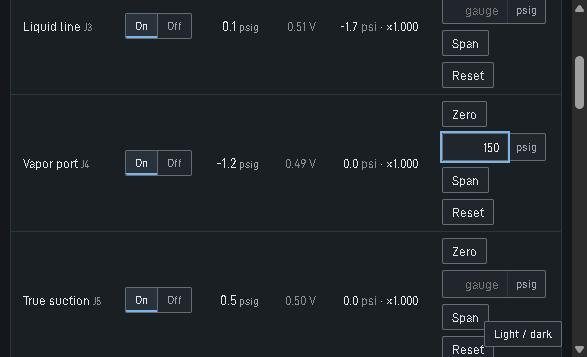
project-files/3-screenshots/3-technician-tools/02-sensors-and-calibration-zero-span.jpg
