mrknockknockgaming-droid/hvac-monitor/project-files/3-screenshots/4-homeowner/01-maintenance-card-due-soon.jpg

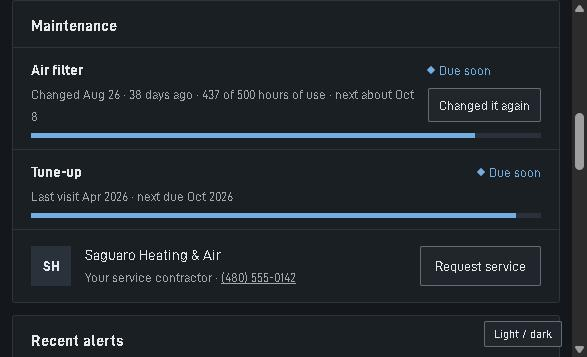
project-files/3-screenshots/4-homeowner/01-maintenance-card-due-soon.jpg
