mrknockknockgaming-droid/hvac-monitor/project-files/3-screenshots/4-homeowner/02-maintenance-card-recent-service.jpg

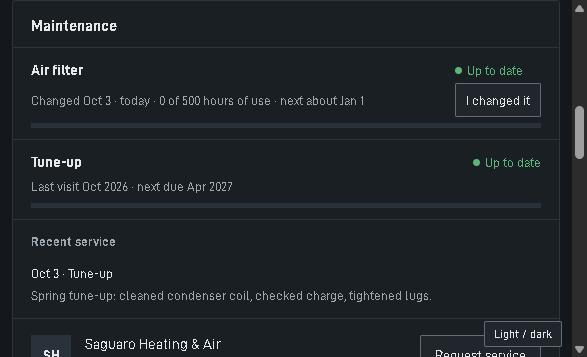
project-files/3-screenshots/4-homeowner/02-maintenance-card-recent-service.jpg
